ciborg971/ProtoBoard/firmware/lucidgloves-firmware/DriverProtocol.hpp

#pragma once

struct EncodedInput {
  enum Type : char {
    THUMB = 'A',
    INDEX = 'B',
    MIDDLE = 'C',
    RING = 'D',
    PINKY = 'E',
    JOY_X = 'F',
    JOY_Y = 'G',
    JOY_BTN = 'H',
    TRIGGER = 'I',
    A_BTN = 'J',
    B_BTN = 'K',
    GRAB = 'L',
    PINCH = 'M',
    MENU = 'N',
    CALIBRATE = 'O'
  };


  // Setup any hardware needed for the input here.
  virtual void setupInput() {};

  // Get the maximum size of the encoded string this input
  // produces
  virtual inline int getEncodedSize() const = 0;

  // Encode the input to a strin the driver can understand.
  virtual int encode(char* output) const = 0;

  // Update internal data from any sensors or whatever the
  // input represents. This should be called every loop.
  virtual void readInput() = 0;
};

struct DecodedOuput {
  enum Type : char {
    FFB_THUMB = 'A',
    FFB_INDEX = 'B',
    FFB_MIDDLE = 'C',
    FFB_RING = 'D',
    FFB_PINKY = 'E',
    HAPTIC_FREQ = 'F',
    HAPTIC_DURATION = 'G',
    HAPTIC_AMPLITUDE = 'H'
  };

  // Setup any hardware needed for the output here.
  virtual void setupOutput() {};

  // This function feeds a string from the driver
  // to the output. The output should update any state
  // if its key is present in the string.
  virtual void decodeToOuput(const char* input) = 0;

  // Use any internal state to update the output.
  // This should be called every loop.
  virtual void updateOutput() = 0;
};

int encodeAll(char* output, EncodedInput* encoders[], size_t count) {
  int offset = 0;
  // Loop over all of the encoders and encode them to the output string.
  for (size_t i = 0; i < count; i++) {
    // The offset is the total charecters already added to the string.
    offset += encoders[i]->encode(output+offset);
  }

  // Add a new line to the end of the encoded string.
  output[offset++] = '\n';
  output[offset] = '\0';

  return offset;
}
