ciborg971/ProtoBoard/firmware/hw-test/config.h

#define MUX_INPUT_A      DirectPin<35>() // Must be a direct pin!
#define MUX_INPUT_B      DirectPin<34>() // Must be a direct pin!
// Ouput pins
#define MUX_SEL_0           26
#define MUX_SEL_1           25
#define MUX_SEL_2           32
#define MUX_SEL_3           33

#define PIN_THUMB_FFB       27
#define PIN_INDEX_FFB       14
#define PIN_MIDDLE_FFB      12
#define PIN_RING_FFB        13
#define PIN_PINKY_FFB       15
